jacobralls4/Ultrasonic-Radio/Comparison image of bodeplot.png

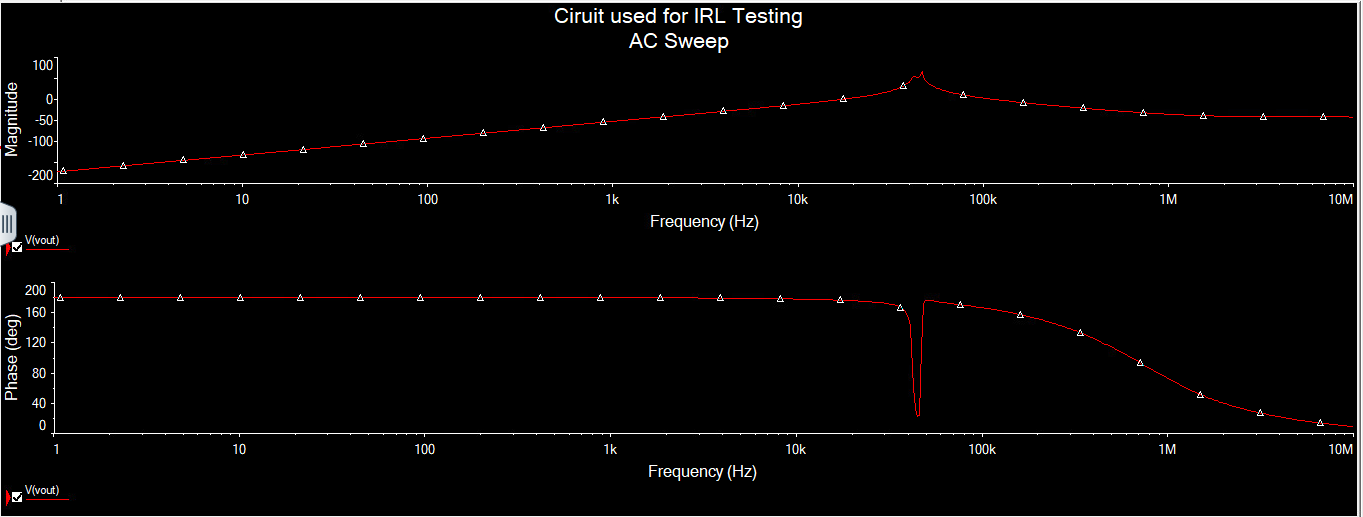
Comparison image of bodeplot.png
