jacobralls4/Ultrasonic-Radio/Expected demodulated output.png

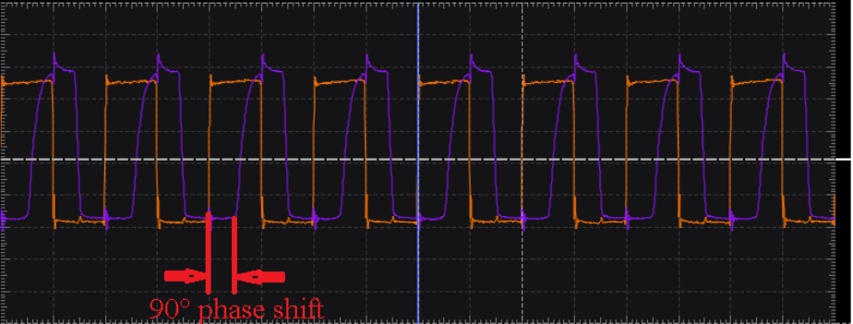
Expected demodulated output.png
