jacobralls4/Ultrasonic-Radio/ModFreq no trans.png

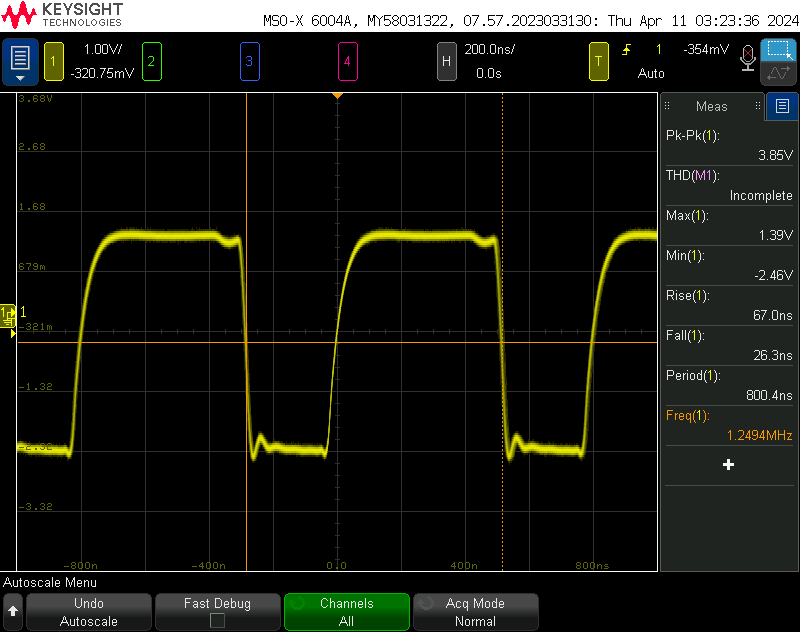
ModFreq no trans.png
