jacobralls4/Ultrasonic-Radio/New.png

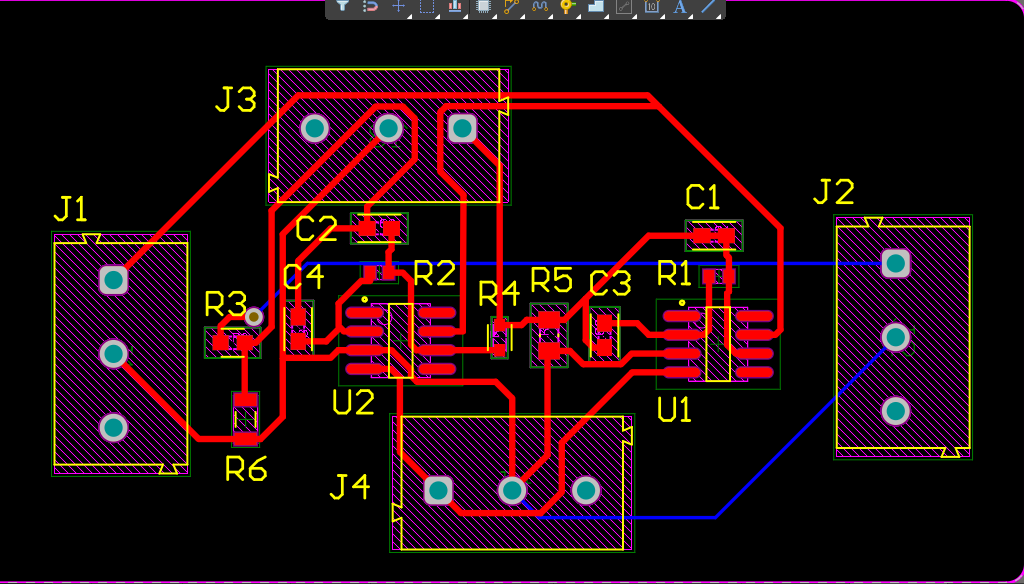
New.png
