jacobralls4/Ultrasonic-Radio/OG.png

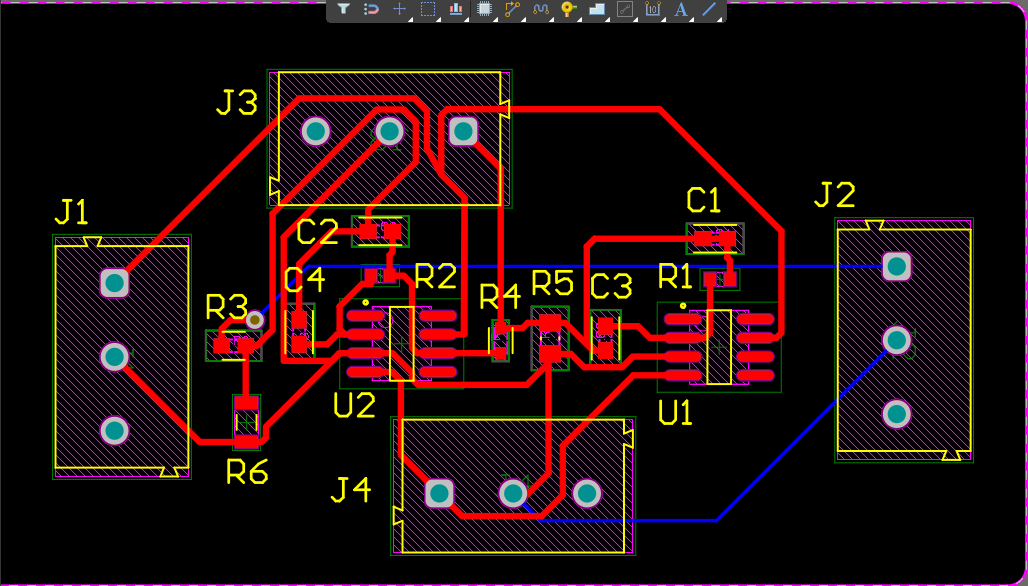
OG.png
