jacobralls4/Ultrasonic-Radio/Tapping output.png

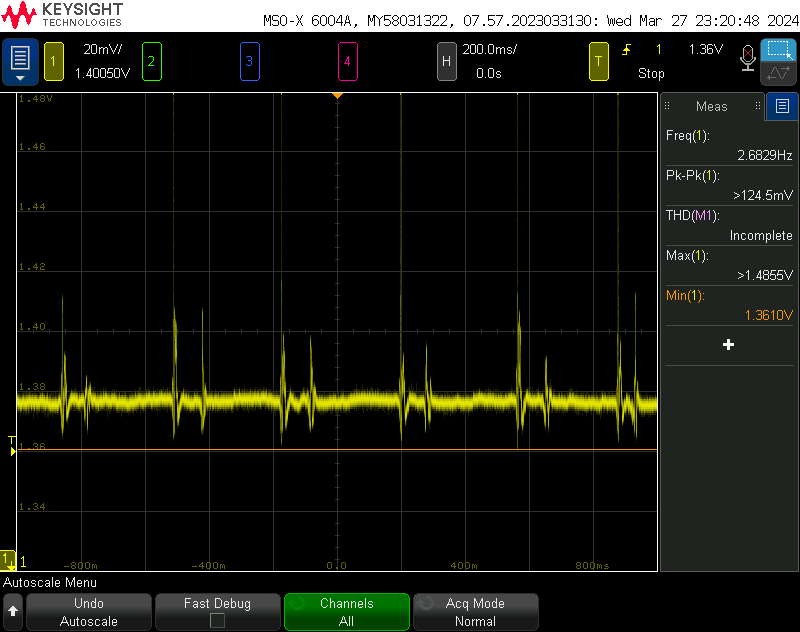
Tapping output.png
