jacobralls4/Ultrasonic-Radio/THD.png

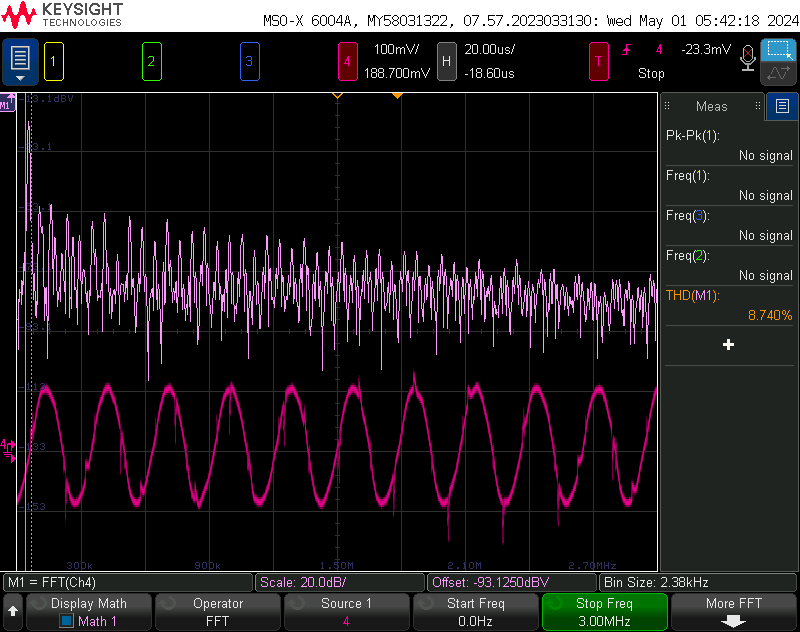
THD.png
