jacobralls4/Ultrasonic-Radio/TransTuner1.png

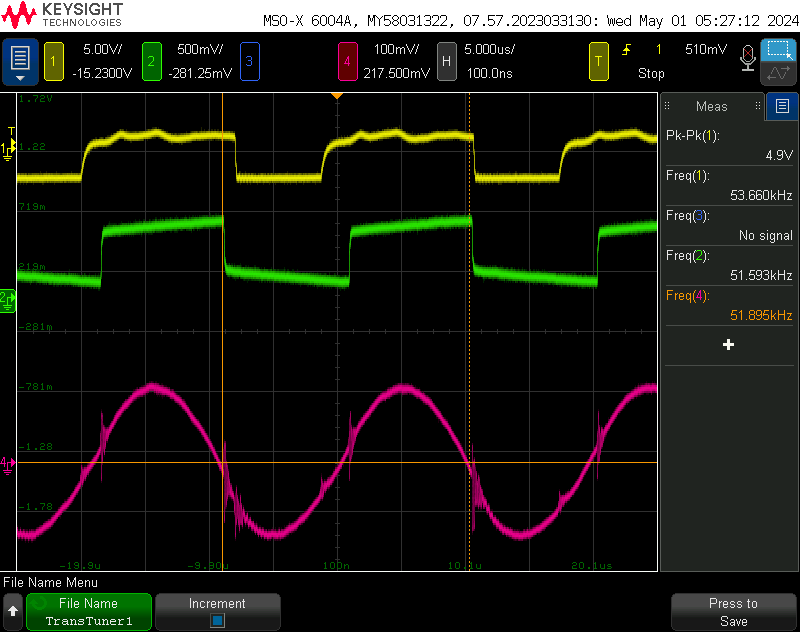
TransTuner1.png
