jacobralls4/Ultrasonic-Radio/TransTuner.png

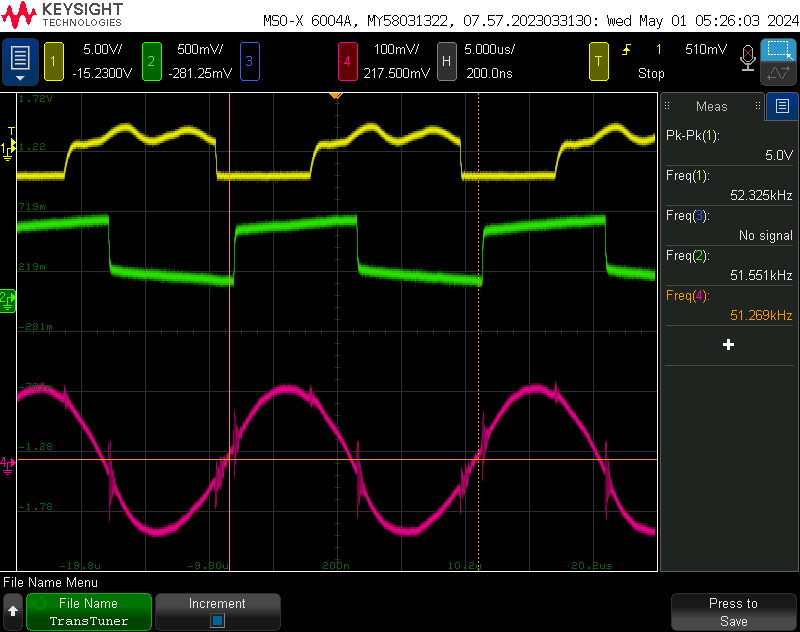
TransTuner.png
