jacobralls4/Ultrasonic-Radio/Waveform of BPF.png

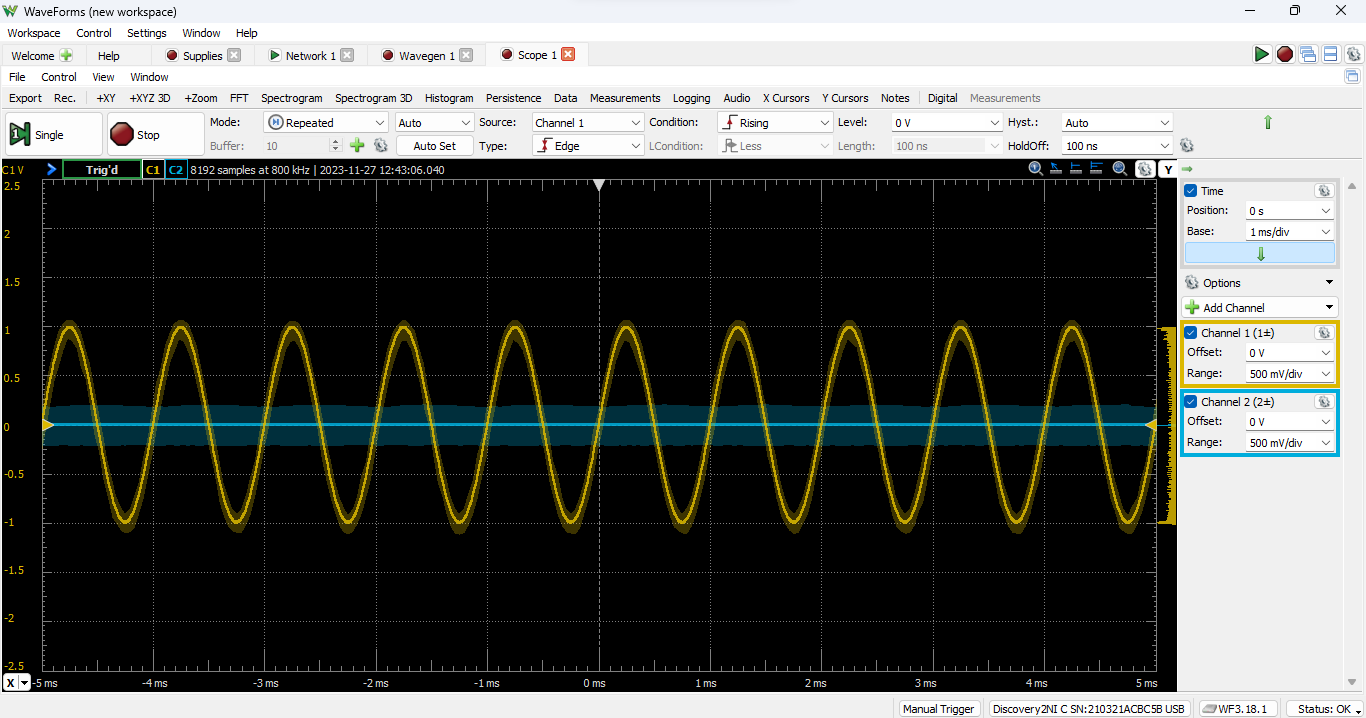
Waveform of BPF.png
