jacobralls4/Ultrasonic-Radio/YTransBlR12GrRecPSpe.png

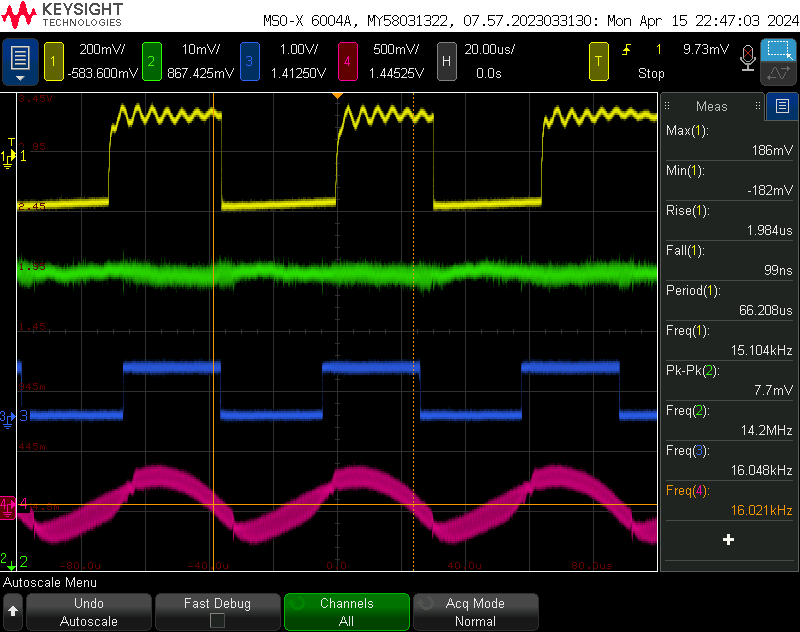
YTransBlR12GrRecPSpe.png
