jacobralls4/Ultrasonic-Radio/YTrGrTunBlRecPiSpe1.png

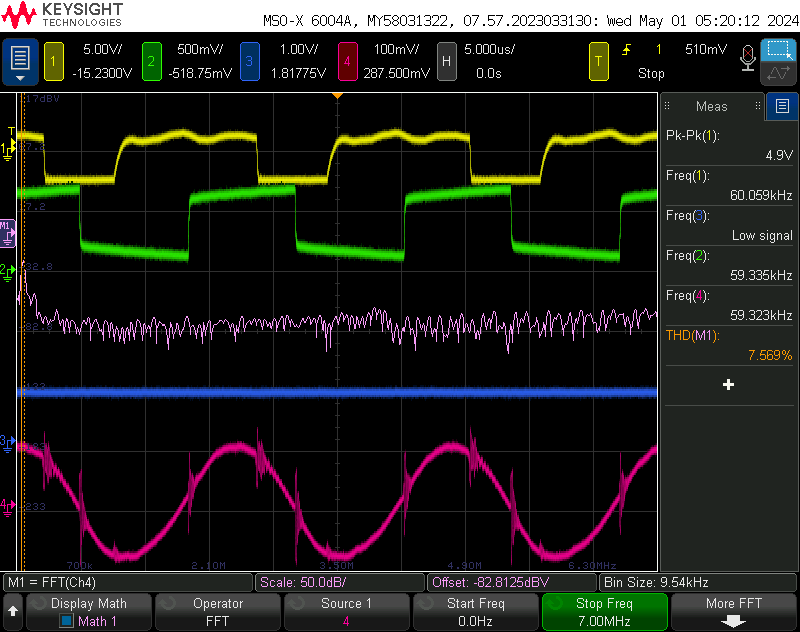
YTrGrTunBlRecPiSpe1.png
