jacobralls4/Ultrasonic-Radio/Circuit Used for irl testing.png

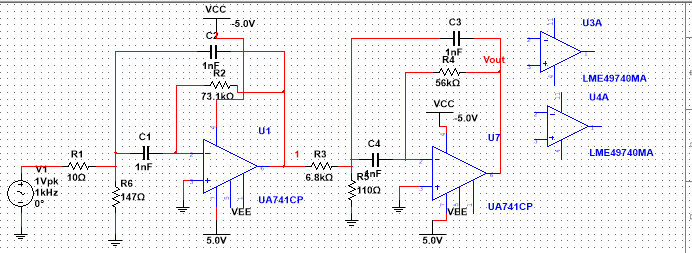
Circuit Used for irl testing.png
