jacobralls4/Ultrasonic-Radio/Image during testing.png

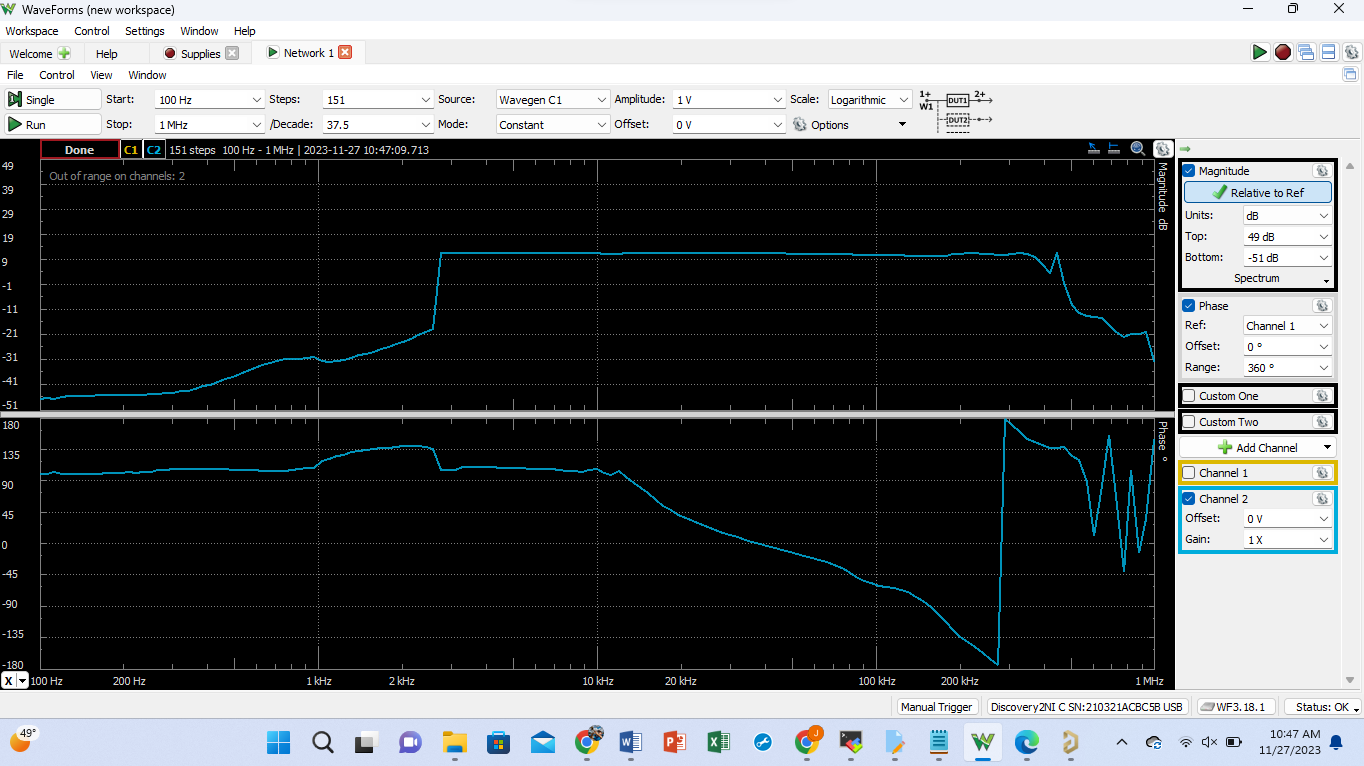
Image during testing.png
