jacobralls4/Ultrasonic-Radio/BandPassFilter2ndOrderBessel.asc

C1: cap; 1n
C2: cap; 1n
R1: res; 2.4k
R2: res; 5.6k
R3: res; 5.9k
R4: res; 1.2k
R5: res; 2.4k
R6: res; 100
R7: res; 300
U1: UniversalOpAmp
U2: LT317A
V1: voltage; SINE(0 1 50k); AC 1 0
V2: voltage; 0
V4: voltage; 9
Named nets: 0, Vin, V++, Vout
;ac dec 100 10 1000000
.tran .0001
;dc dec 100 10 1000000
