jacobralls4/Ultrasonic-Radio/BandpassFilter6thorderBessel(WORKS BUT GOES DOWN TO 10kHz).asc

C1: cap; 1n
C2: cap; 1n
C3: cap; 1n
C4: cap; 1n
C5: cap; 1n
C6: cap; 1n
R1: res; 2.26k
R2: res; 8.06k
R3: res; 2.21k
R4: res; 5.36k
R5: res; 2.49k
R6: res; 1.69k
R7: res; 2.49k
R8: res; 1.69k
R9: res; 2.49k
R10: res; 9.53k
R11: res; 2k
R12: res; 5.9k
R13: res; 11k
R14: res; 1.65k
R15: res; 2.94k
U1: UniversalOpAmp
U2: UniversalOpAmp
U3: UniversalOpAmp
V1: voltage; SINE(0 1 50k); AC 1 0
V2: voltage; -5
V3: voltage; 5
Named nets: 0
.ac dec 100 .2 200k
;tran 0.0001
