jacobralls4/Ultrasonic-Radio/Draft1.asc

C1: cap; 10p
C2: cap; 1n
C3: cap; 10p
C4: cap; 1n
R1: res; 1000
R2: res; 14300
R3: res; 75k
R4: res; 6.8k
R5: res; 11500
R6: res; 59k
U1: UniversalOpAmp
U2: UniversalOpAmp
V1: voltage; SINE(0 1 1k); AC 1 0
V2: voltage; -5
V3: voltage; 5
V4: voltage; -5
V5: voltage; 5
Named nets: 0, Vout, Vin
;ac dec 100 0.2 200k
.tran 0.01
