jacobralls4/Ultrasonic-Radio/Draft2.asc

C1: cap; 0.1µ
L1: ind; 1000
M2: nmos4; TSMC180nmN; l=360n w=100u
R1: res; 50k
R2: res; 130k
R3: res; 50k
V1: voltage; 1.8
Vtest: voltage; SINE(0 30m 10k); AC 1 0
Named nets: 0, Vout, Vgate, Vsource, test
.include C:\\Users\\jacob\\OneDrive\\Documents\\4thYearSpring\\Undergraduate\\ECEN 471\\Lab2\\TSMC180nm.lib
;op
;ac dec 101 1 10Meg
.tran 500u
