jacobralls4/Ultrasonic-Radio/Draft3.asc

M1: nmos4; TSMC180nmN; 180nmN l=180n w=400n
V1: voltage; 1.8
V2: voltage; 1.8
Named nets: 0
.include C:\\Users\\jacob\\OneDrive\\Documents\\4thYearSpring\\Undergraduate\\ECEN 471\\Lab2\\TSMC180nm.lib
.dc V2 0 1.8 0.02 V1 0 1.8 0.2
