jacobralls4/Ultrasonic-Radio/HighFreq.asc

C1: cap; 390p
C2: cap; 390p
R1: res; 162k
R2: res; 8.06k
R3: res; 698
U1: UniversalOpAmp1
V1: voltage; SINE(0 1 1k); AC 1 0
V2: voltage; 5
V3: voltage; 5
Named nets: 0
;ac dec 100 0.2 200k
.tran 0.01
