jacobralls4/Ultrasonic-Radio/Modulator.asc

C1: cap; 1n
C2: cap; 10µ
C3: cap; 1n
C4: cap; 33n
C5: cap; 1n
C6: cap; 3µ
L1: ind; 500m
L2: ind; 1m
Q1: npn; 2N3904
R1: res; 33k
R2: res; 1.5k
R3: res; 10000
R4: res; 10k
V1: voltage; SINE(0 10 1k)
V2: voltage; 5
Named nets: 0, Vout
.tran 100m
