jacobralls4/Ultrasonic-Radio/NotGateAnalog.asc

D1: LED
Q1: npn; 2N3904
R1: res; 470
R2: res; 10k
V1: voltage; 5
V2: voltage; 0
Named nets: 0, Vout
.op
