jacobralls4/Ultrasonic-Radio/WorkingBPF.asc

C1: cap; 63p
C2: cap; 63p
R1: res; 50k
R2: res; 50k
V1: voltage; SINE(0 1 1k); AC 1 0
Named nets: 0, out, in
.ac dec 100 0.2 200k
